knopsl/StereoOutKosmo/Hardware/PCB/ao_output/ao_output.sch

## KiCad design Hardware/PCB/ao_output/ao_output.sch (2021-09-21)

Schematic: ao_output.sch

Parts:
C1, C2, C3, C4: 470nF; C_Rect_L7.2mm_W2.5mm_P5.00mm_FKS2_FKP2_MKS2_MKP2
C5, C6: 330pF; C_Disc_D3.0mm_W1.6mm_P2.50mm
C7, C8, C9: 2.2uF; C_Radial_D5.0mm_H7.0mm_P2.00mm
C10, C11: 1uF; C_Rect_L7.2mm_W2.5mm_P5.00mm_FKS2_FKP2_MKS2_MKP2
D1, D2, D3, D4, D5, D6, D7, D8: 1N5817; D_DO-41_SOD81_P7.62mm_Horizontal
GRAF1: Holes layout; ao_output_panel_slide_holes
GRAF3: AO logo; analogoutput
GRAF4: OSHW logo; OSHW-Logo2_7.3x6mm_SilkScreen
H1, H2, H3, H4: MountingHole; MountingHole_3.2mm_M3
J1: Conn_02x05_Odd_Even; PinSocket_2x05_P2.54mm_Vertical
J2: Conn_01x17; PinSocket_1x17_P2.54mm_Vertical
J3, J4, J5, J6, J7, J8: AudioJack2; Jack_6.35mm_PJ_629HAN
J9: AudioJack3; Jack_6.35mm_PJ_629HAN
R1, R2, R3, R4, R5, R6, R7, R8, R19, R20: 100k; R_Axial_DIN0207_L6.3mm_D2.5mm_P10.16mm_Horizontal
R9, R10, R11, R12, R13, R14, R15, R16, R17, R18: 10k; R_Axial_DIN0207_L6.3mm_D2.5mm_P10.16mm_Horizontal
R21, R22, R23, R24: 3.9k; R_Axial_DIN0207_L6.3mm_D2.5mm_P10.16mm_Horizontal
R25, R26: 33k; R_Axial_DIN0207_L6.3mm_D2.5mm_P10.16mm_Horizontal
R27, R28: 75R 1/2 W; R_Axial_DIN0309_L9.0mm_D3.2mm_P12.70mm_Horizontal
R29, R30: 1k; R_Axial_DIN0207_L6.3mm_D2.5mm_P10.16mm_Horizontal
U1: TL074; DIP-14_W7.62mm_Socket_LongPads
U2: TL072; DIP-8_W7.62mm_Socket_LongPads
U3: LM4808; SOIC-8_3.9x4.9mm_P1.27mm

Notes on the sheet:
Main board
Socket not actually fitted, solder pins from slide pots board header. THIS IS STUPID. DON'T DO IT THIS WAY.
Actually it would be better to have sliders and jacks on the same board, main circuit on another.
