knopsl/StereoOutKosmo/Hardware/PCB/ao_output/power_and_panel.sch

## KiCad design Hardware/PCB/ao_output/power_and_panel.sch (2021-03-18)

Schematic: power_and_panel.sch

Parts:
C12, C13: 10uF; CP_Radial_D5.0mm_P2.00mm
C14, C15, C16, C17, C19, C20: 100nF; C_Disc_D3.0mm_W1.6mm_P2.50mm
C18: 330nF; C_Disc_D3.0mm_W1.6mm_P2.50mm
D9, D10: 1N5817; D_DO-41_SOD81_P7.62mm_Horizontal
GRAF2: Holes layout; ao_output_panel_slide_holes
H3, H4: MountingHole; MountingHole_3.2mm_M3
J10: Synth_power_2x5; Power_Header
J11: Conn_02x05_Odd_Even; PinHeader_2x05_P2.54mm_Vertical
J12: Conn_01x17; PinHeader_1x17_P2.54mm_Vertical
RV1, RV2, RV3, RV4: B100k; Potentiometer_Alpha_RA6020F_Single_Slide
RV5, RV6, RV7, RV8, RV9: B10k; Potentiometer_Alpha_RD902F-40-00D_Dual_Vertical_CircularHol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
U1: TL074; DIP-14_W7.62mm_Socket_LongPads
U2: TL072; DIP-14_W7.62mm_Socket_LongPads
U3: LM4808; SOIC-8_3.9x4.9mm_P1.27mm
U4: L78L05_TO92; TO-92_Inline
