knopsl/StereoOutKosmo/Hardware/Panel/ao_output_panel/ao_output_panel.sch

## KiCad design Hardware/Panel/ao_output_panel/ao_output_panel.sch (2021-04-02)

Schematic: ao_output_panel.sch

Parts:
GRAF1: Holes; ao_output_panel_slide_holes
GRAF2: Art; ao_output_panel_slide_art
H1, H2, H3, H4, H5, H6, H7: MountingHole_Pad; Kosmo_Jack_Hole
H8, H9, H10, H11, H12: MountingHole_Pad; Kosmo_Pot_Hole
H13, H14, H15, H16: MountingHole_Pad; Kosmo_Panel_Slotted_Mounting_Hole
H17, H18, H19, H20: MountingHole_Pad; Kosmo_Panel_Mounting_Hole
